w5xd/WWVBclock/PCB/Keystone103.FCStd

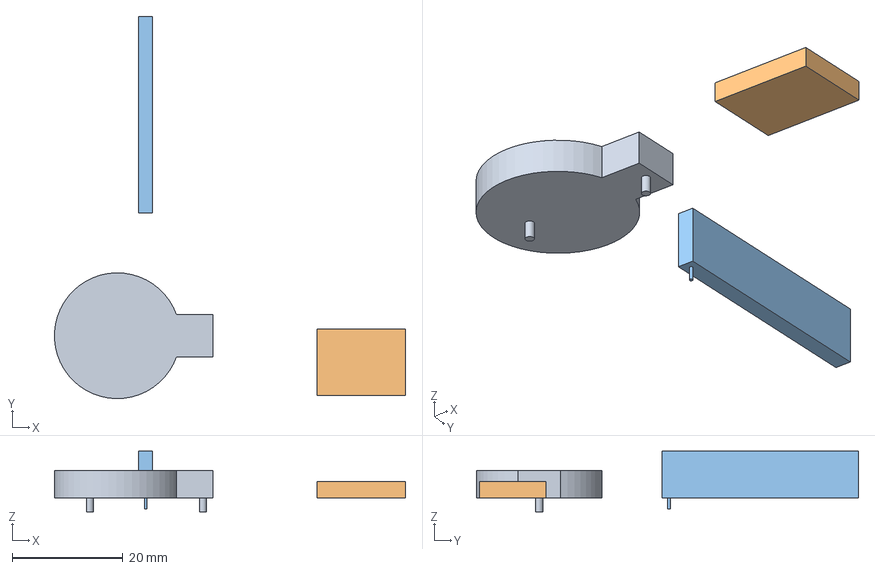
[picture p16: CAD file, 2025-05-17]
PCB/Keystone103.FCStd
63.5 x 69.2 x 11.0 mm
coin cell holder
PSK receiver
Teensy header
