w5xd/WWVBclock/CAD/step/Retainer ring_1.stp

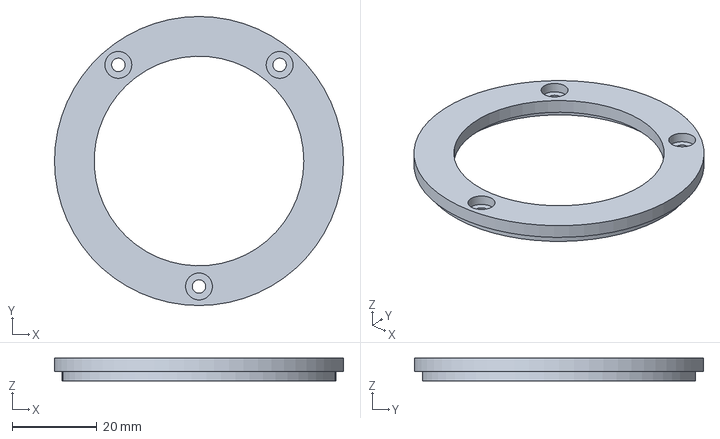
[picture p17: CAD file, 2025-05-17]
CAD/step/Retainer ring_1.stp
68.3 x 68.3 x 5.33 mm
