w5xd/WWVBclock/PCB/PRPC007DAAN_RC.stp

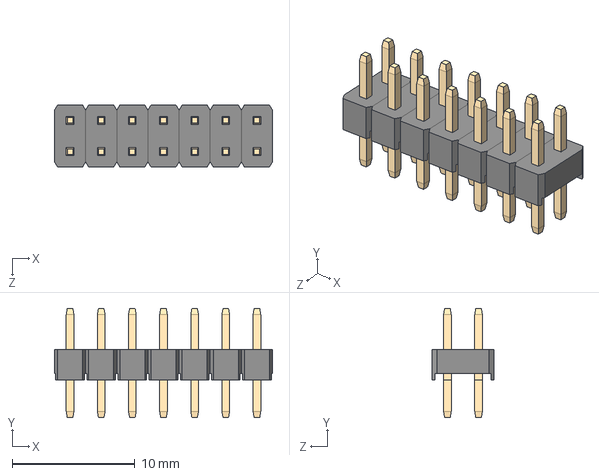
[picture p18: CAD file, 2025-05-17]
PCB/PRPC007DAAN_RC.stp
17.8 x 8.89 x 5.08 mm
PREC001DAAN-RC_C07
Pin - Gold_AA x 7
