w5xd/WWVBclock/CAD/step/Nameplate.stp

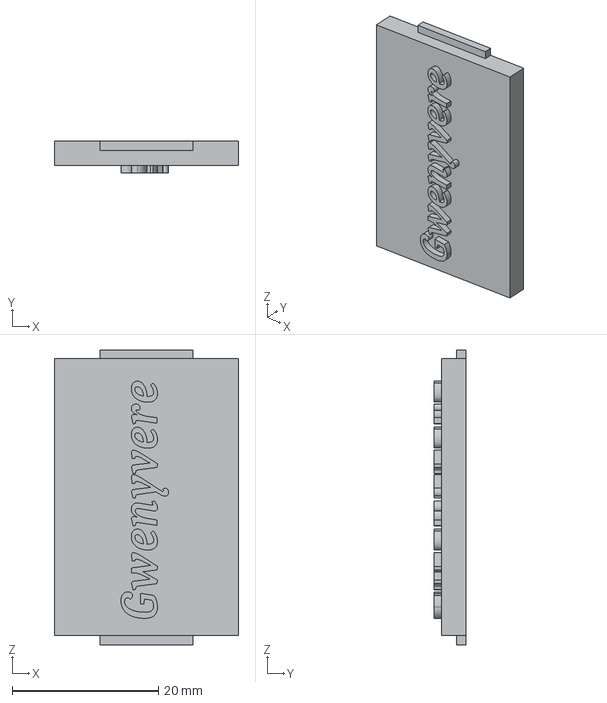
[picture p19: CAD file, 2025-05-17]
CAD/step/Nameplate.stp
25.1 x 4.32 x 40.3 mm
