w5xd/WWVBclock/PCB/SwitchFSM12JH.stp

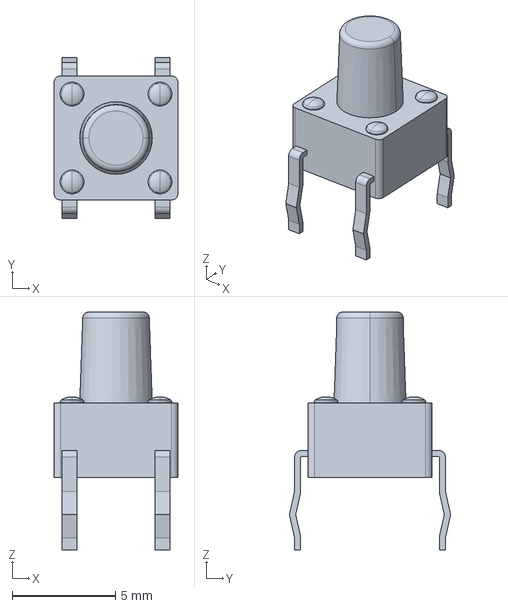
[picture p20: CAD file, 2025-05-17]
PCB/SwitchFSM12JH.stp
5.99 x 7.80 x 11.5 mm
